WBLundFLA/teabag-caddy/files/caddy_front.scad

// ============================================================
//  caddy_front.scad  —  FRONT HALF (drawer-opening side)
//  Render: F6   Export: File → Export → STL → caddy_front.stl
// ============================================================
include <caddy_params.scad>

caddy_half(is_front = true);
